FordyceLab/micrio/timing/data/bf.png

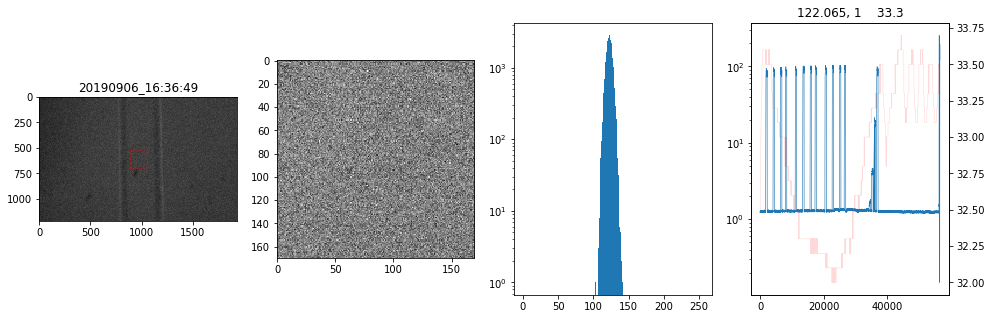
timing/data/bf.png
