FordyceLab/micrio/timing/data/bf_20190906-1637.png

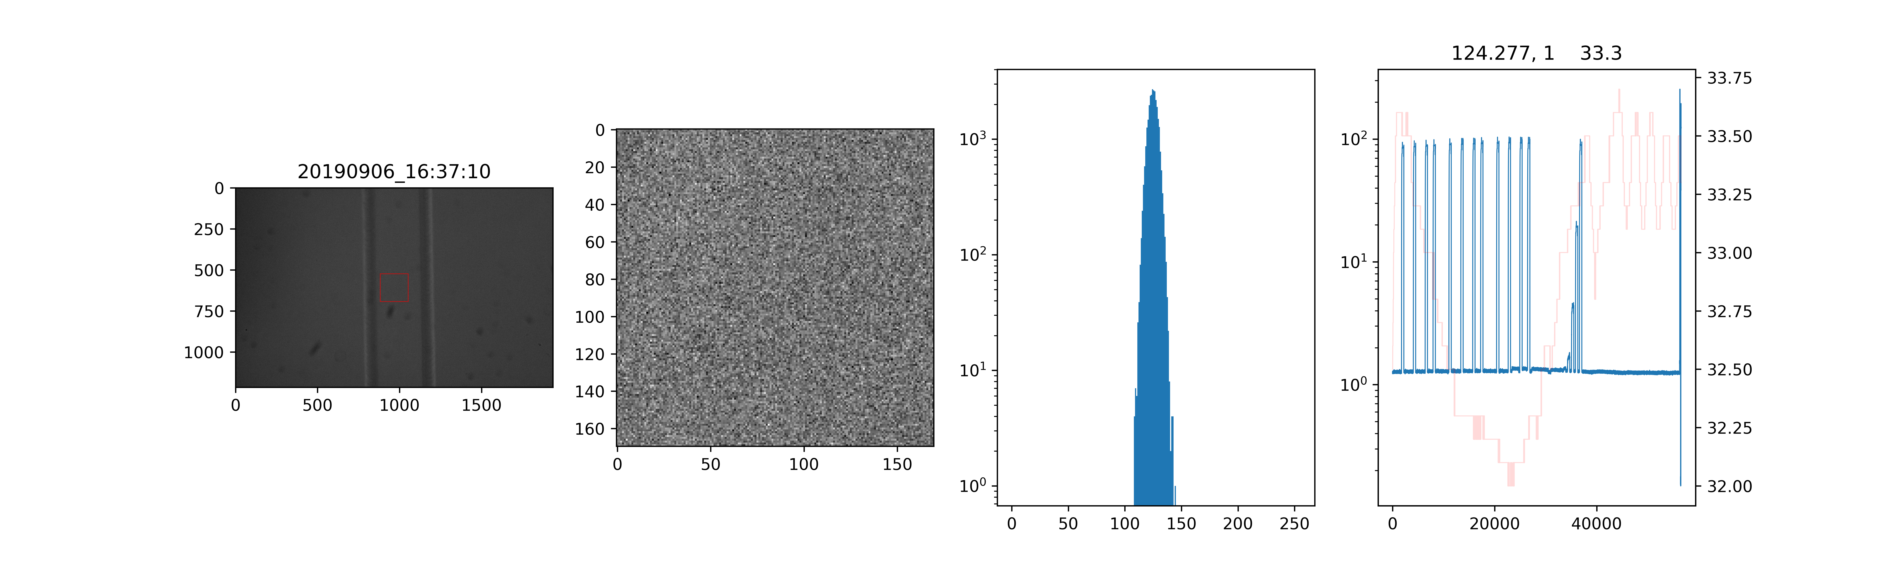
timing/data/bf_20190906-1637.png
