FordyceLab/micrio/timing/data/fluor.png

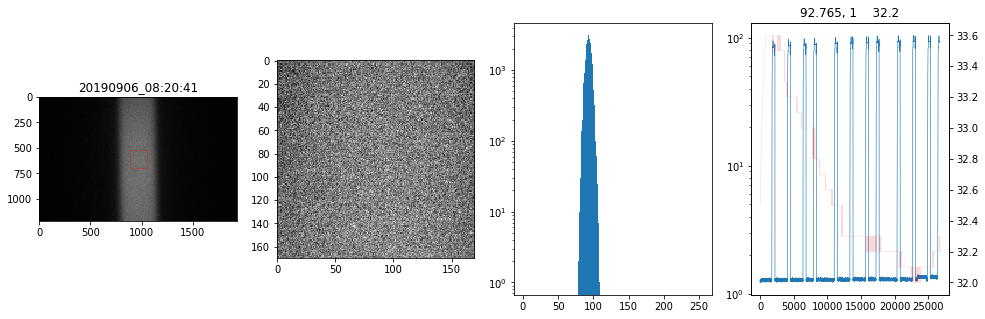
timing/data/fluor.png
